ep092/server_lader/Bilder/Masse gebrückt Übersicht.jpg

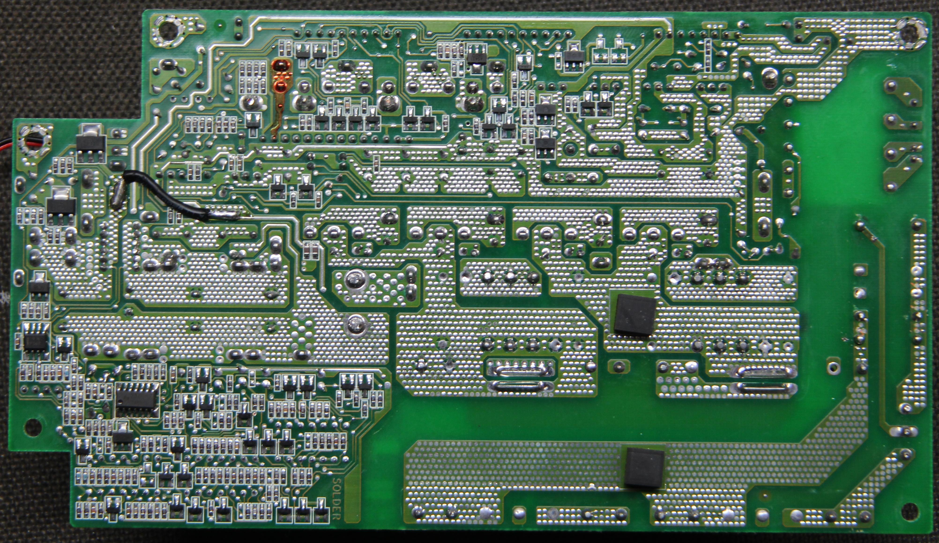
Bilder/Masse gebrückt Übersicht.jpg
