ep092/server_lader/Bilder/P1050215.JPG

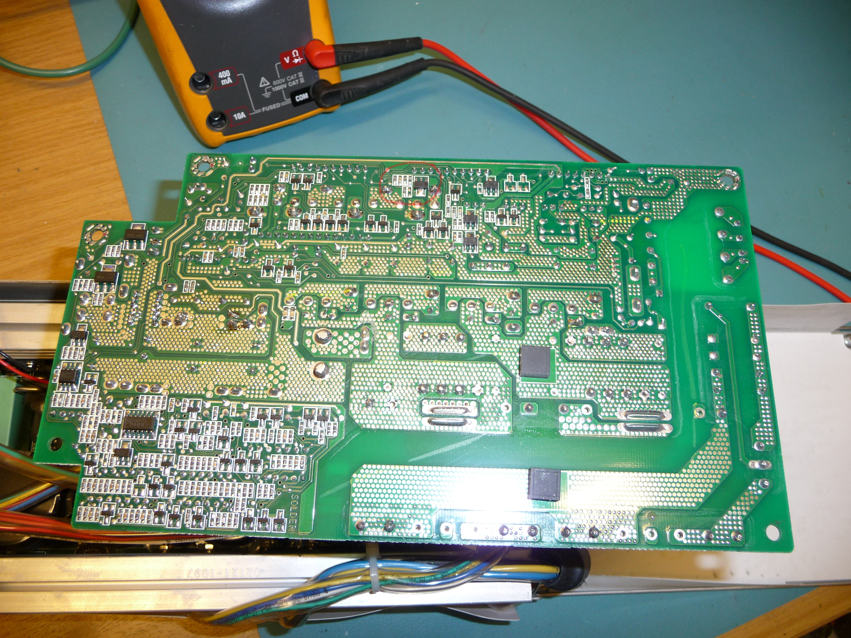
Bilder/P1050215.JPG
