ep092/server_lader/Bilder/P1050216.JPG

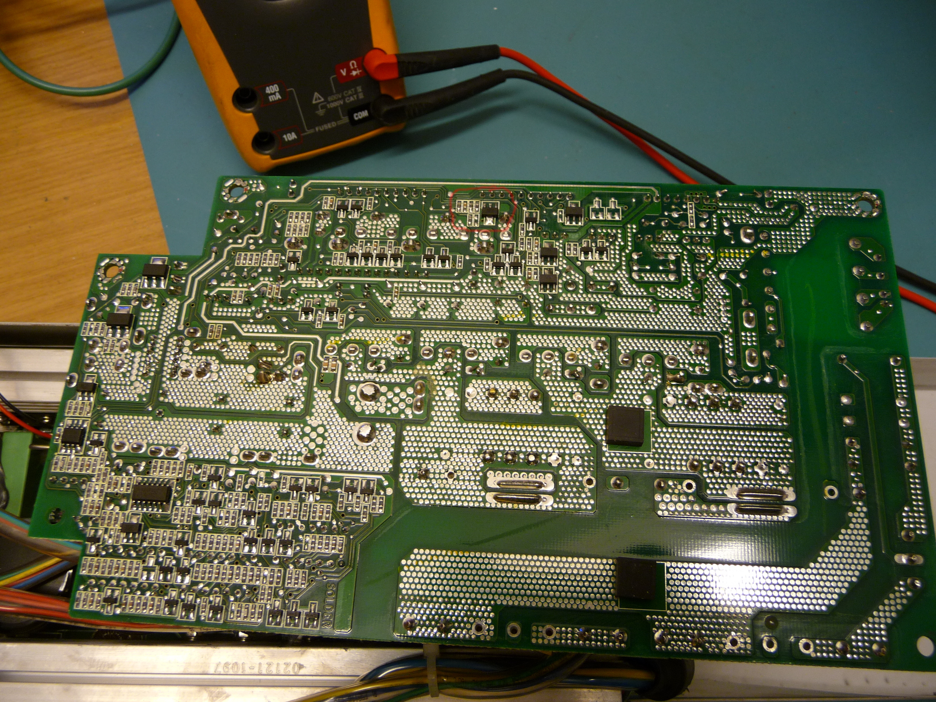
Bilder/P1050216.JPG
