ep092/server_lader/Bilder/P1050217.JPG

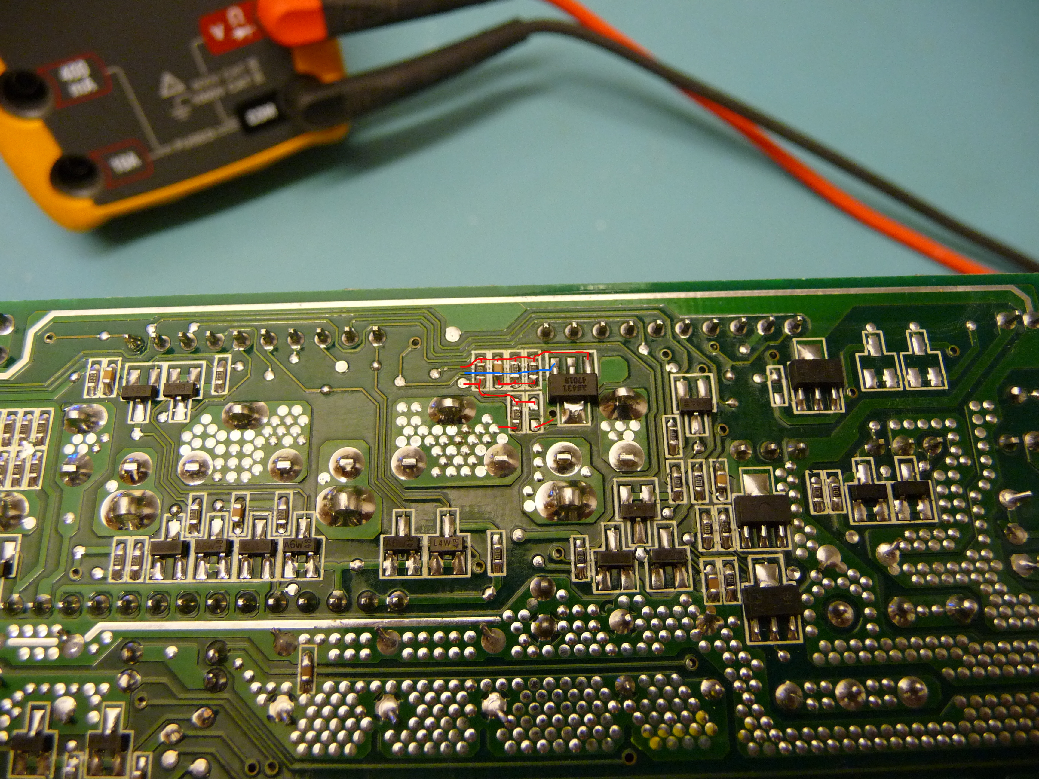
Bilder/P1050217.JPG
