ep092/server_lader/Bilder/P1050219.JPG

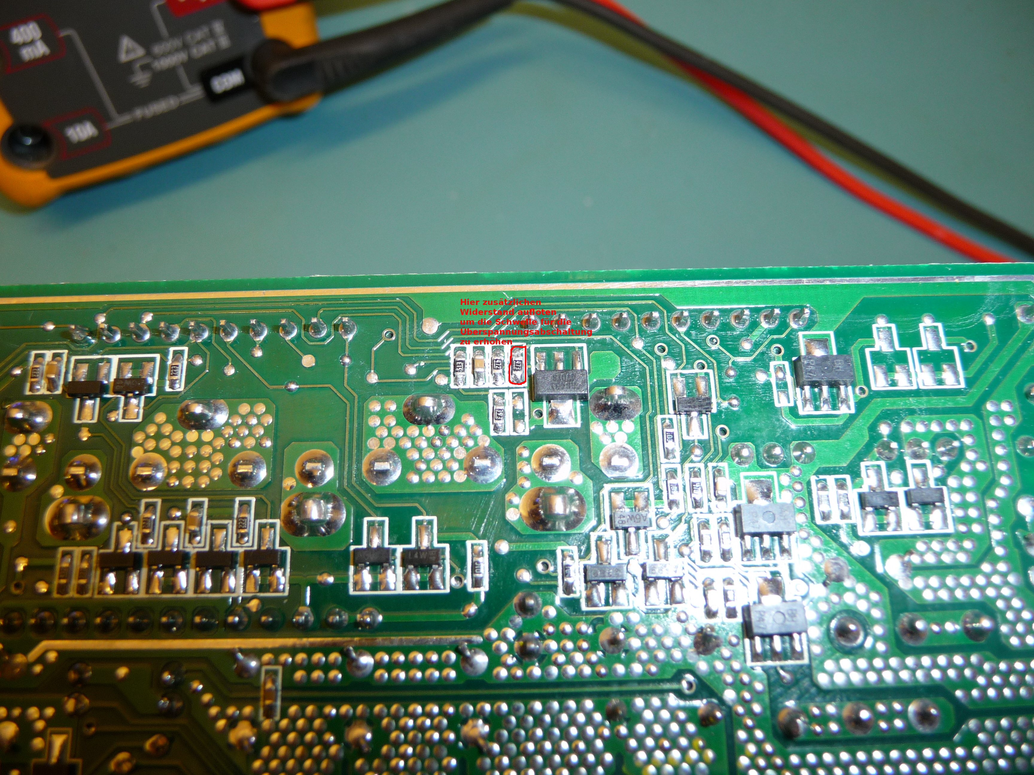
Bilder/P1050219.JPG
