ep092/server_lader/Bilder/P1050221.JPG

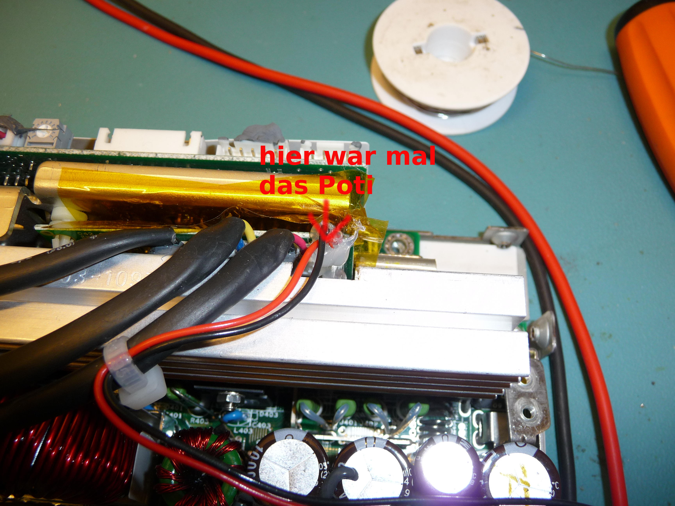
Bilder/P1050221.JPG
