ep092/server_lader/Bilder/Aufbau_phil_1_seitlich.JPG

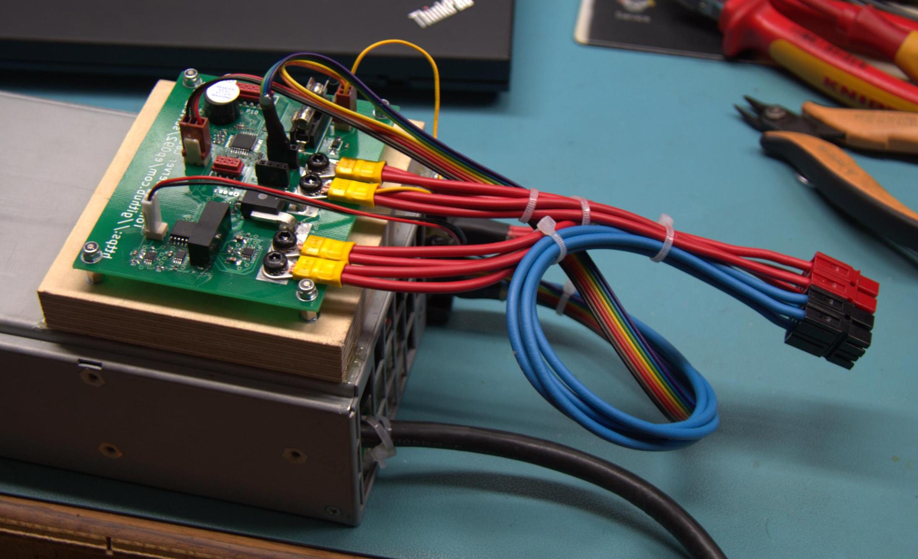
Bilder/Aufbau_phil_1_seitlich.JPG
