ep092/server_lader/Bilder/Testaufbau_1_Übersichtsbild.jpg

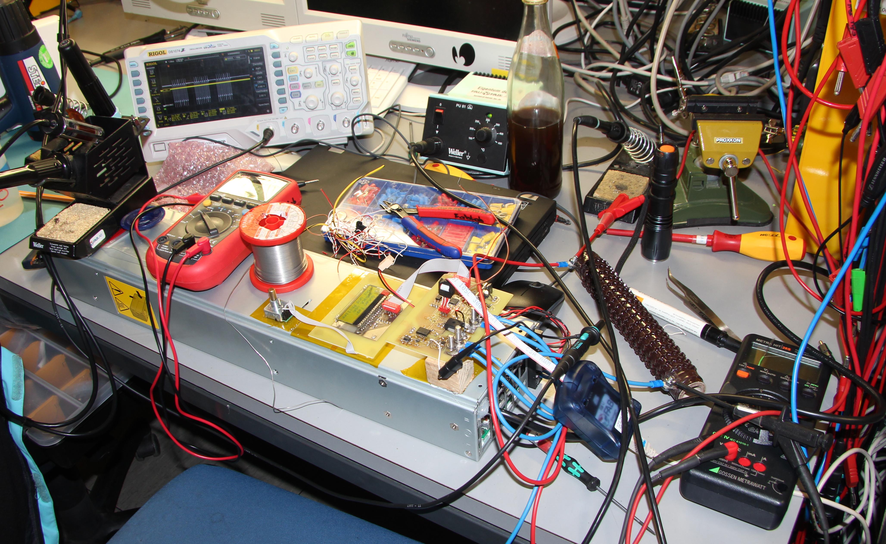
Bilder/Testaufbau_1_Übersichtsbild.jpg
