ep092/server_lader/Bilder/Testaufbau_3_Regelteil.jpg

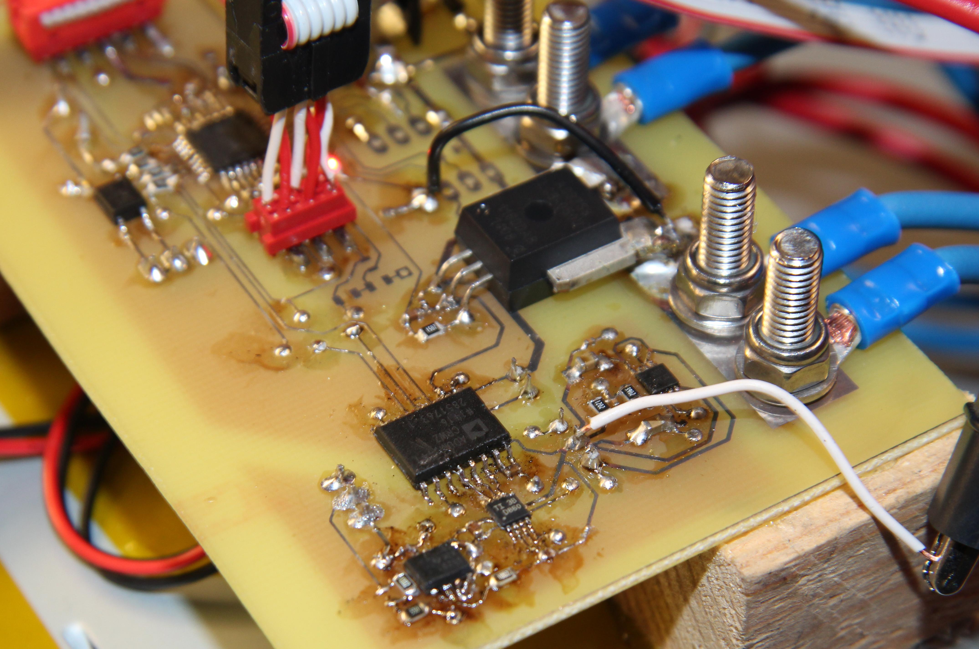
Bilder/Testaufbau_3_Regelteil.jpg
